akuehlewind/ESPHome-touch-display-mount/esphome/buttons/images/smartdisplay_background_90.png

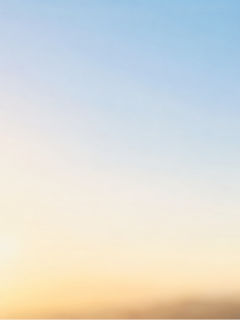
esphome/buttons/images/smartdisplay_background_90.png
